EmilSchaetzle/PI-Book/case/PIBookCoverPart3.stl

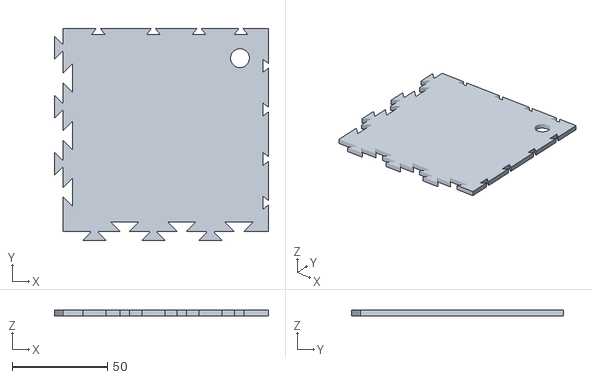
[picture p28: CAD file, 2019-02-14]
case/PIBookCoverPart3.stl
112.5 x 111.2 x 3.00
