EmilSchaetzle/PI-Book/case/PIBookTopPart3.stl

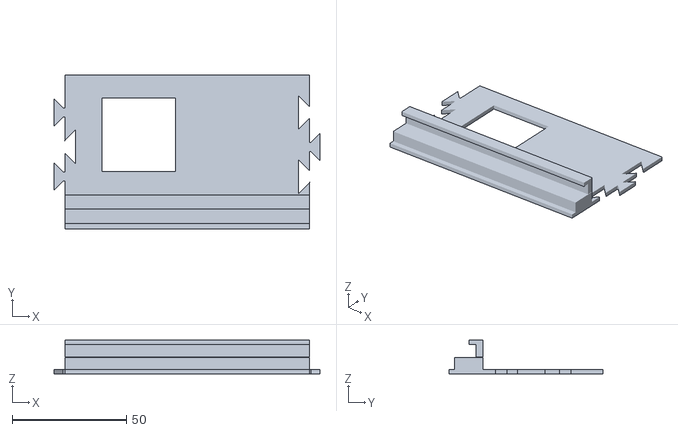
[picture p29: CAD file, 2019-02-14]
case/PIBookTopPart3.stl
116.2 x 67.5 x 14.9
