EmilSchaetzle/PI-Book/case/PIBookTopPart1.stl

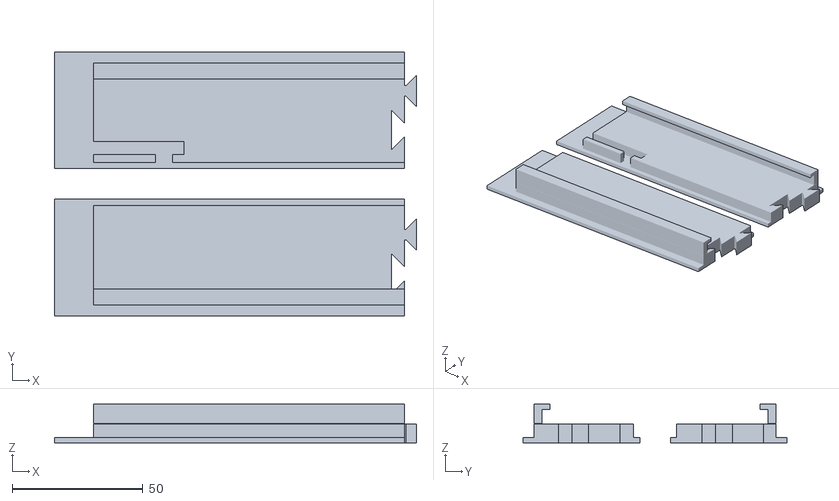
[picture p30: CAD file, 2019-02-14]
case/PIBookTopPart1.stl
138.6 x 101.0 x 14.9
